Katell-Lag/robot_nageur/controle_robot/Trinamic/TMC6100-EVAL-KIT/Setup/Capture1.PNG

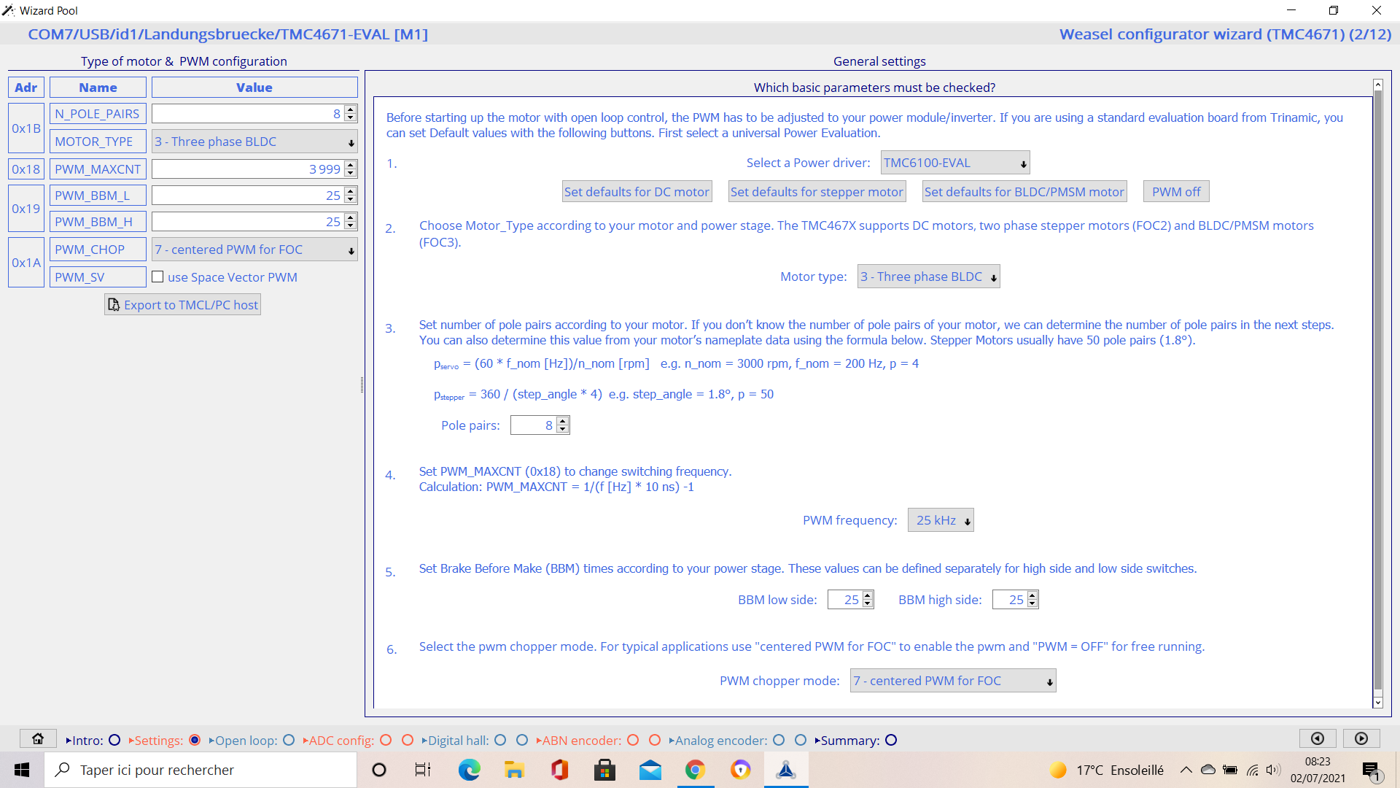
controle_robot/Trinamic/TMC6100-EVAL-KIT/Setup/Capture1.PNG
